monty124/AnalogVoltMeterClock/Back Panel/Back Panel 1.png

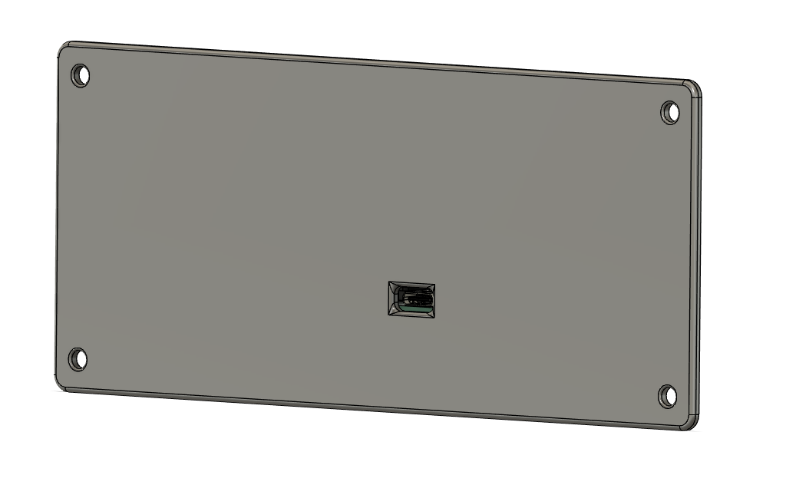
Back Panel/Back Panel 1.png
