monty124/AnalogVoltMeterClock/Back Panel/Back Panel 2.png

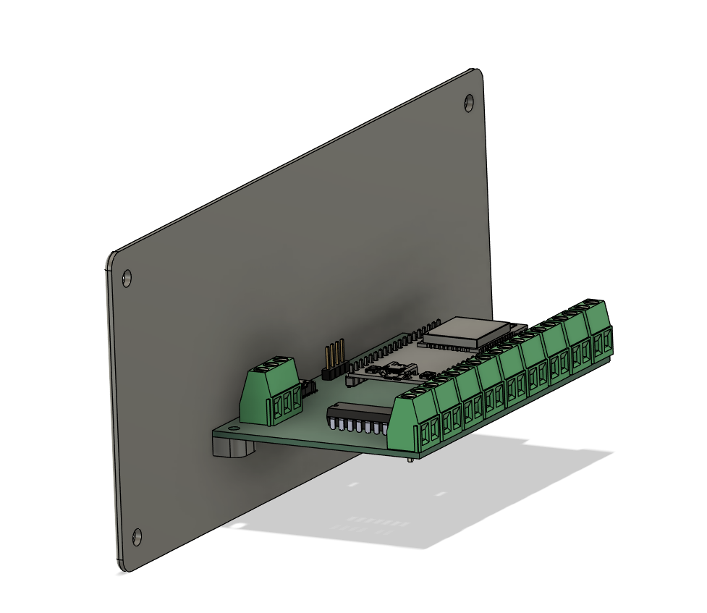
Back Panel/Back Panel 2.png
