monty124/AnalogVoltMeterClock/Back Panel/Dimensions.png

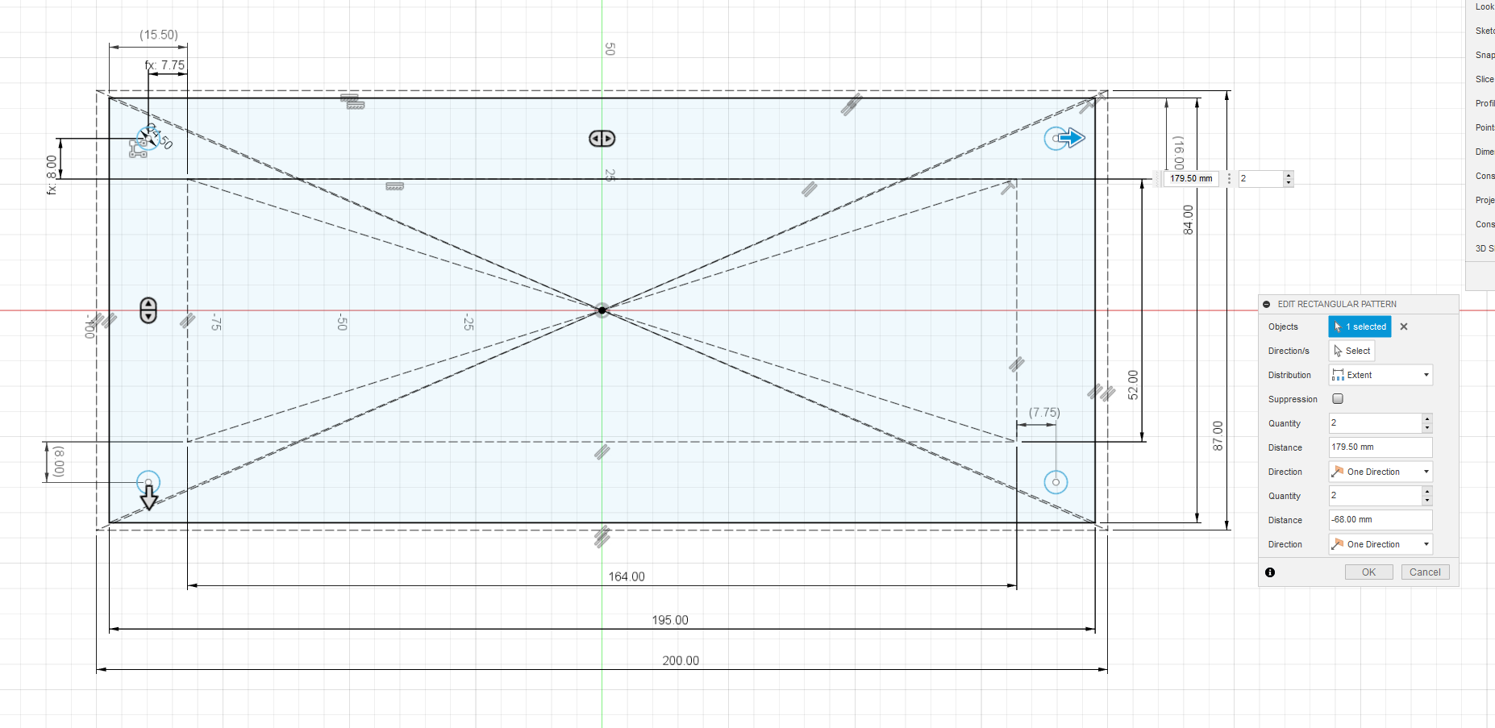
Back Panel/Dimensions.png
